C442/Rocket/Deployment mechanism/Nose Cone Inspo/images/4be0d2e7-f49b-4930-87dd-065aca3783c3.png

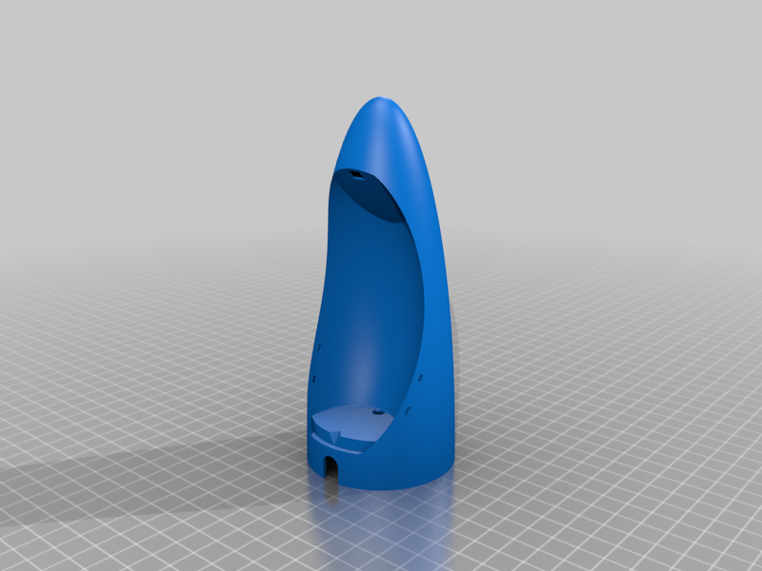
Deployment mechanism/Nose Cone Inspo/images/4be0d2e7-f49b-4930-87dd-065aca3783c3.png
