C442/Rocket/Sketches/Plan_suggestion.png

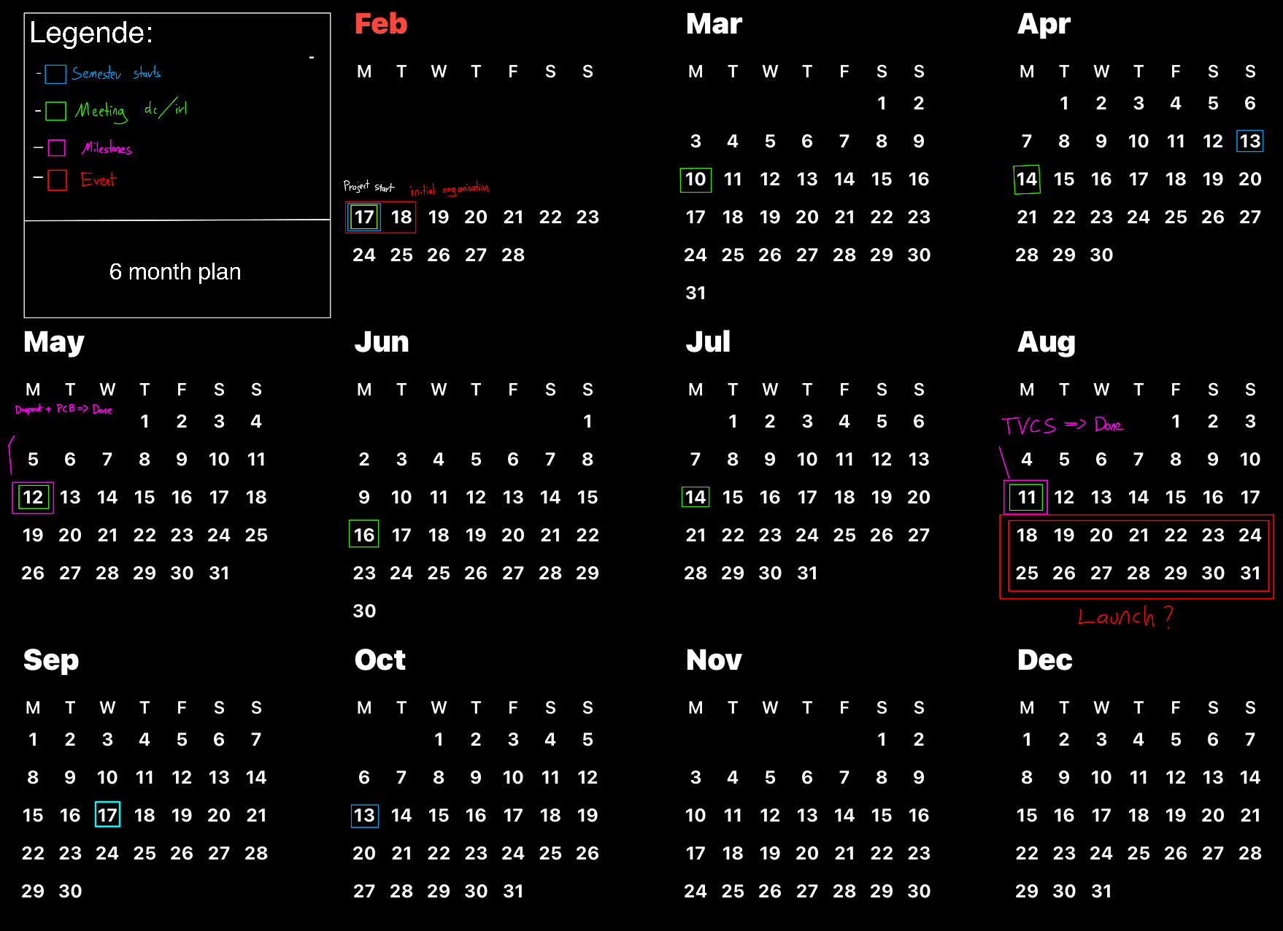
Sketches/Plan_suggestion.png
