C442/Rocket/Sketches/Sugegstion_work.png

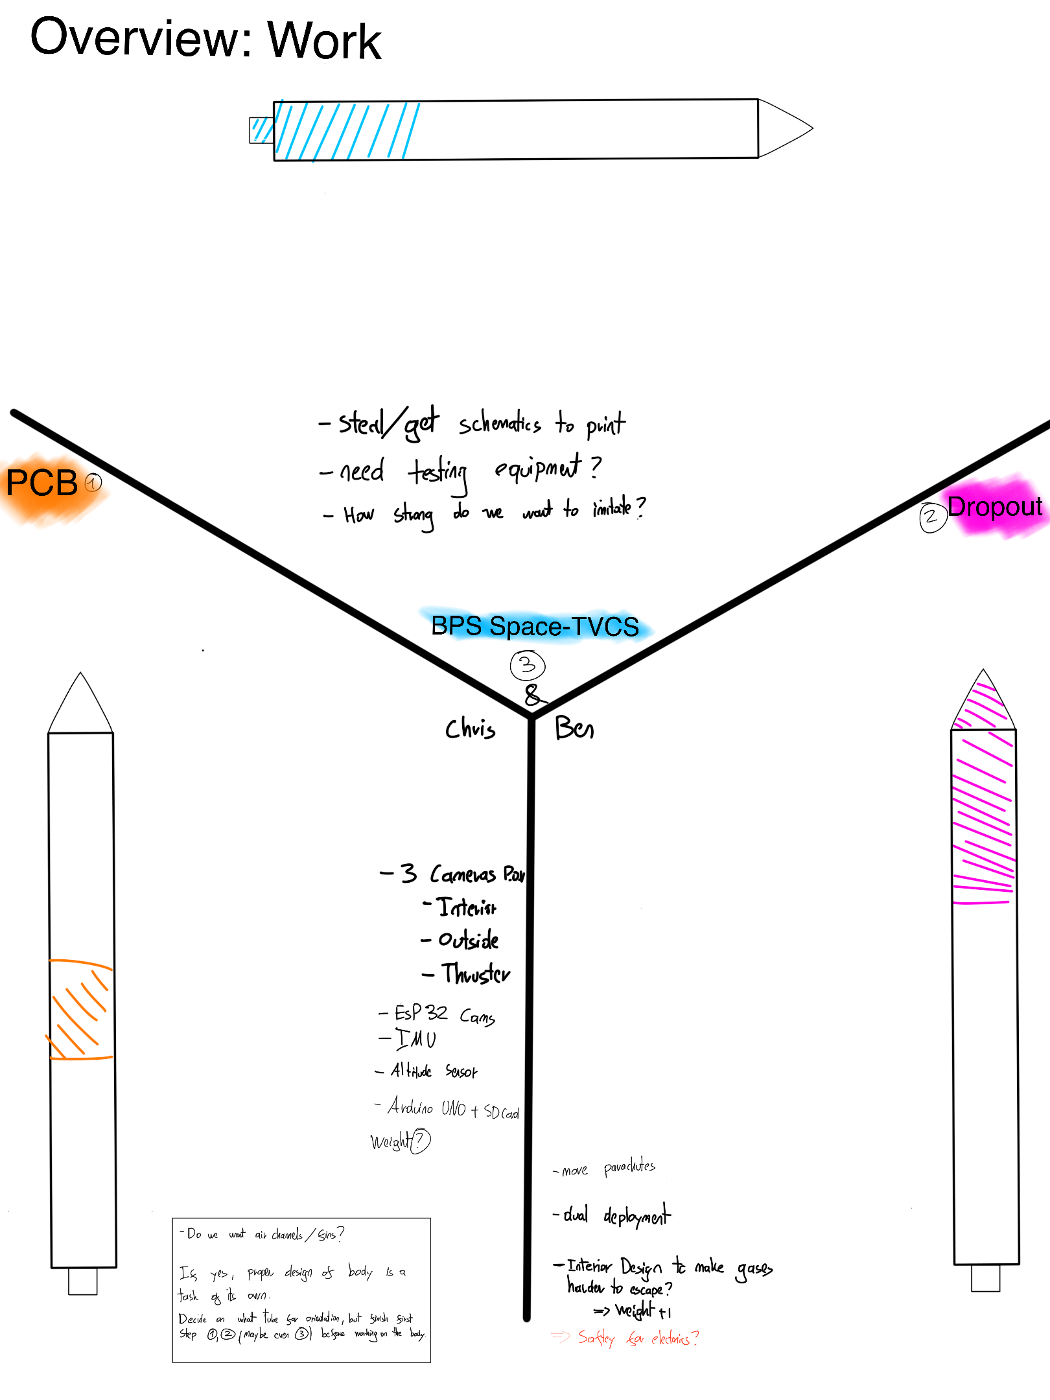
Sketches/Sugegstion_work.png
