C442/Rocket/Sketches/suggestion_visual.png

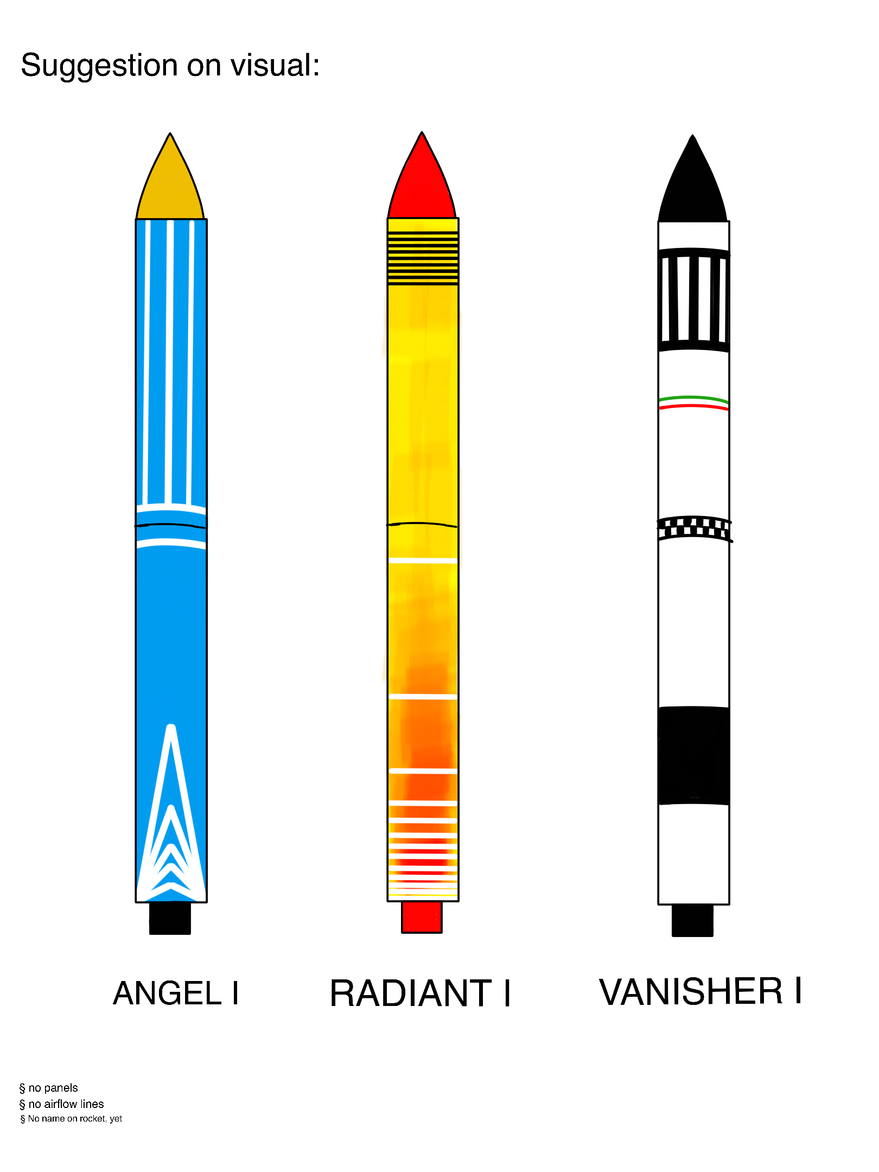
Sketches/suggestion_visual.png
