C442/Rocket/Sketches/thumbnail.jpg

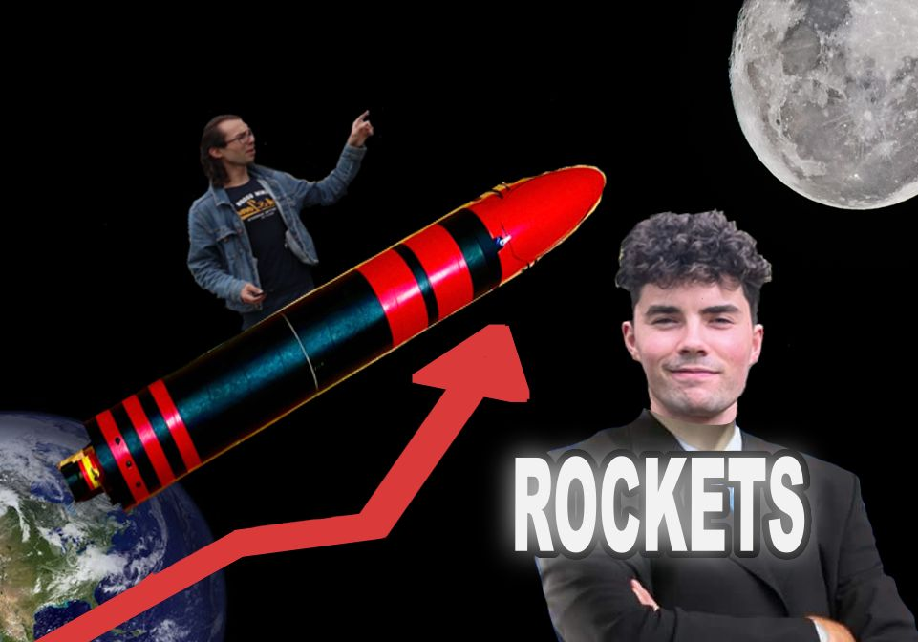
Sketches/thumbnail.jpg
