C442/Rocket/TVC/Second_PID/Inner.png

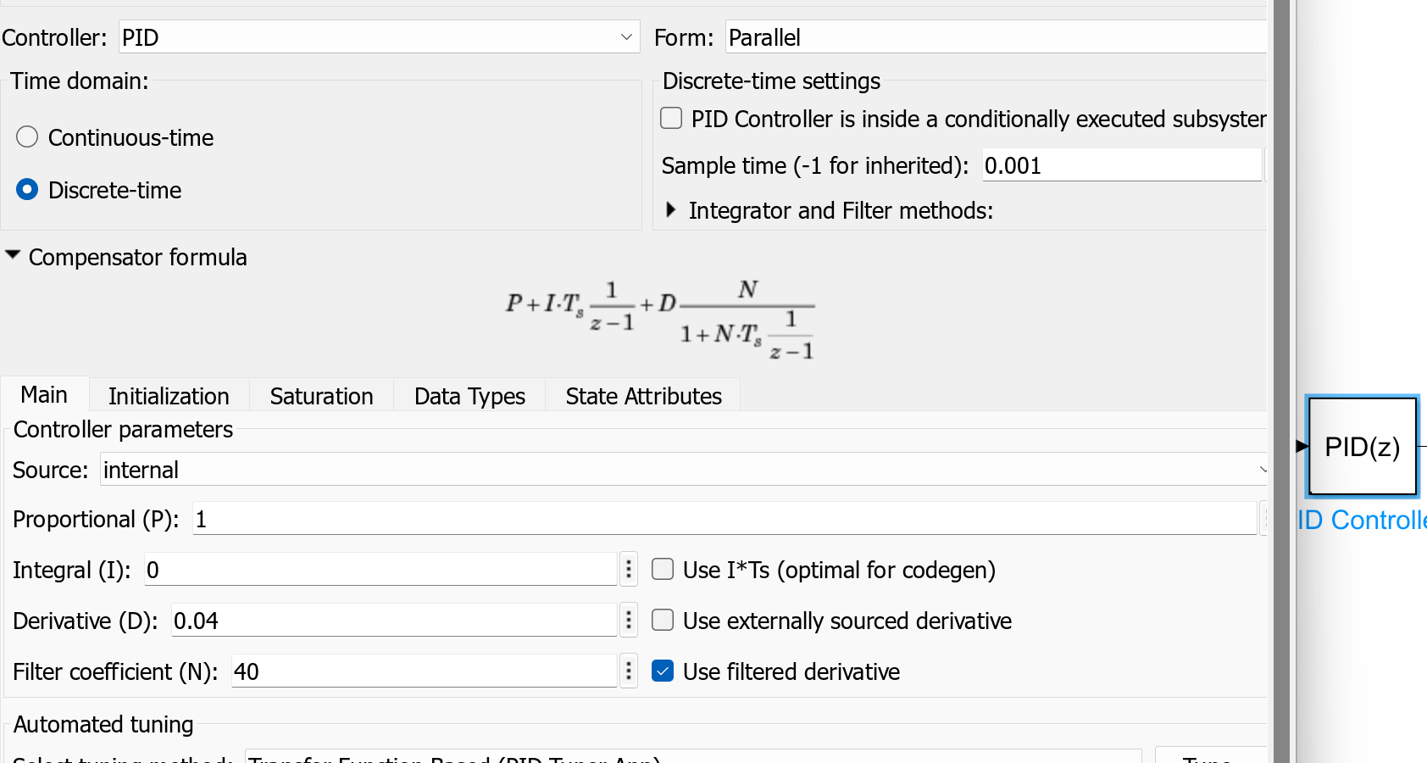
TVC/Second_PID/Inner.png
