C442/Rocket/TVC/Second_PID/Outer.png

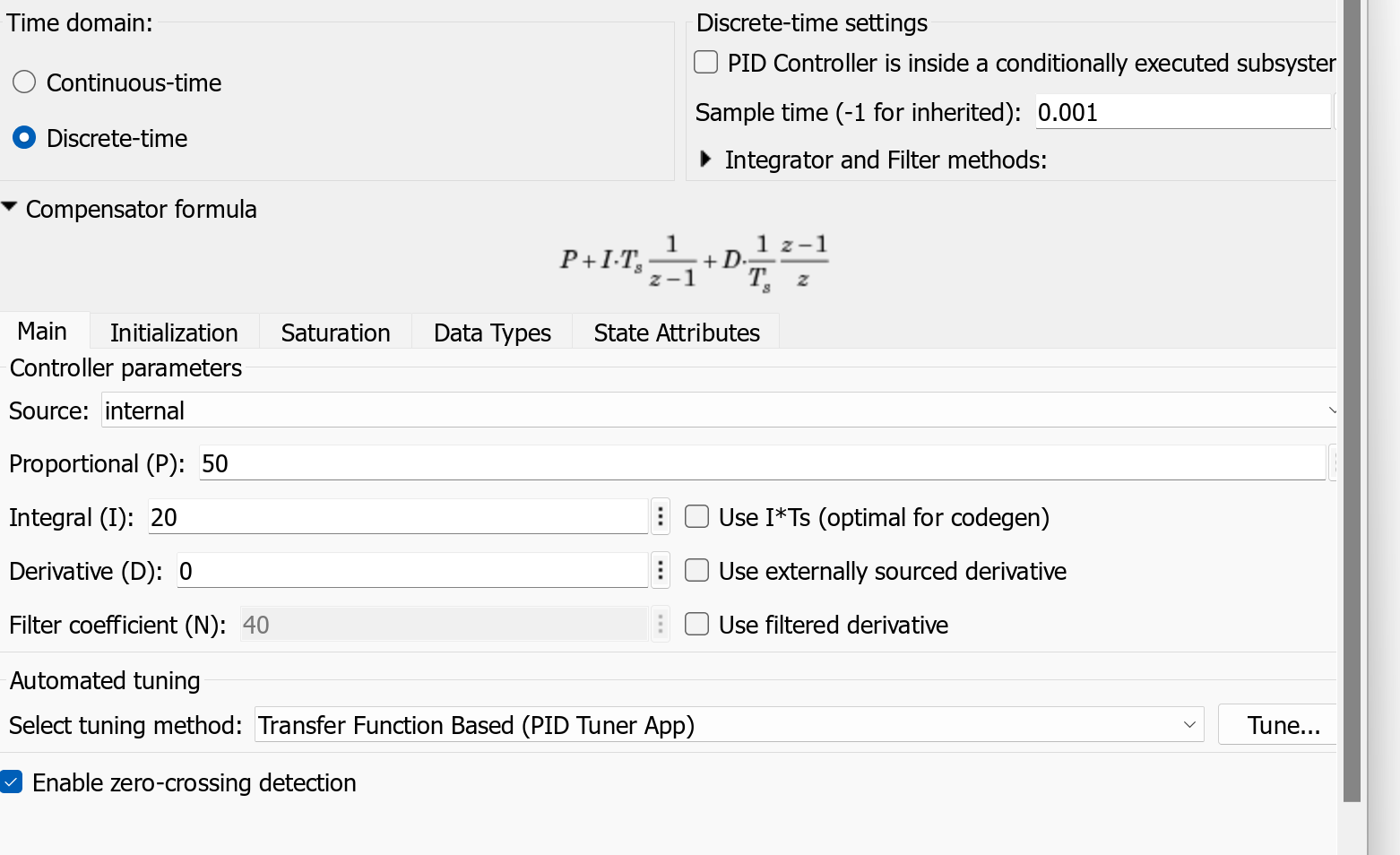
TVC/Second_PID/Outer.png
