C442/Rocket/Deployment mechanism/Nose Cone Inspo/files/retain.stl

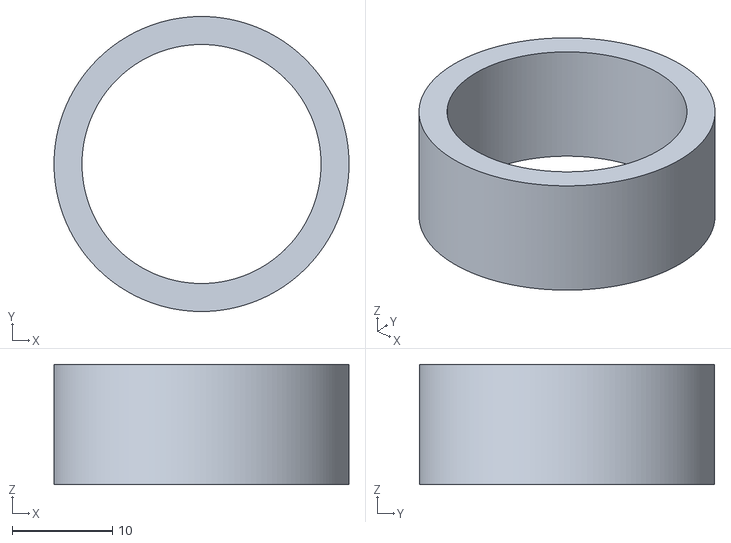
[picture p78: CAD file, 2025-03-27]
Deployment mechanism/Nose Cone Inspo/files/retain.stl
29.5 x 29.5 x 12.0
