C442/Rocket/TVC/Design/Casing.stl

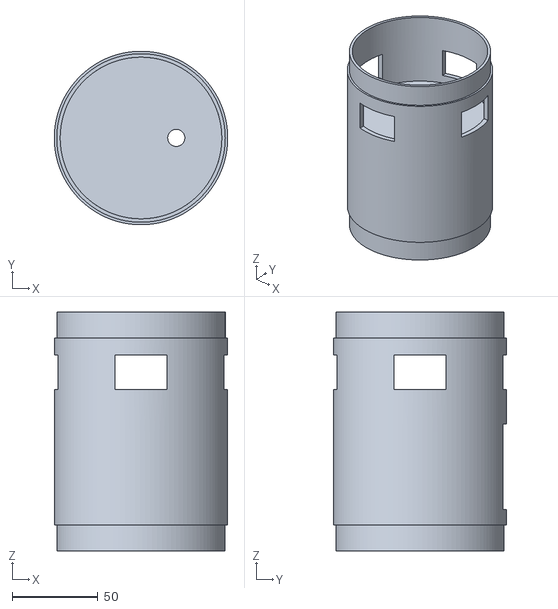
[picture p79: CAD file, 2025-04-25]
TVC/Design/Casing.stl
100.9 x 100.9 x 139.0
