C442/Rocket/Deployment mechanism/Nose Cone Adjusted 15cm/New Base.stl

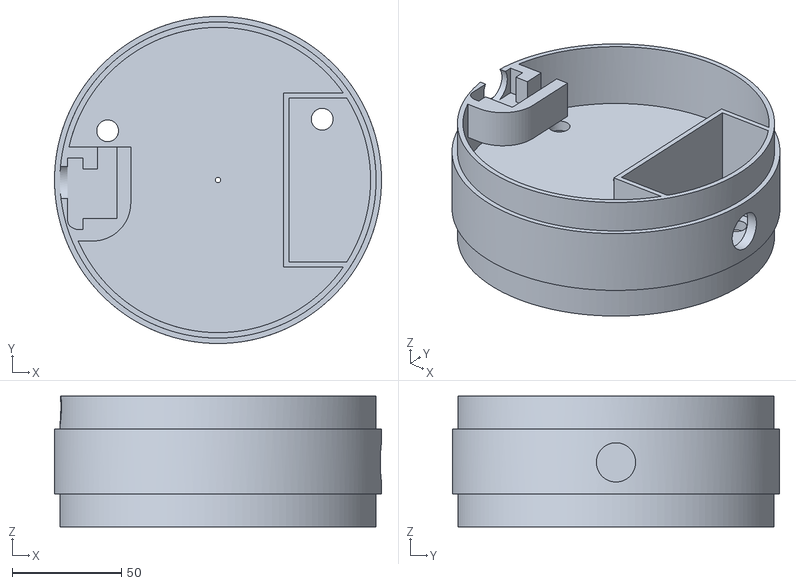
[picture p80: CAD file, 2025-03-27]
Deployment mechanism/Nose Cone Adjusted 15cm/New Base.stl
150.0 x 150.0 x 60.0
