C442/Rocket/Deployment mechanism/Nose Cone Inspo/files/New Nose Cone.stl

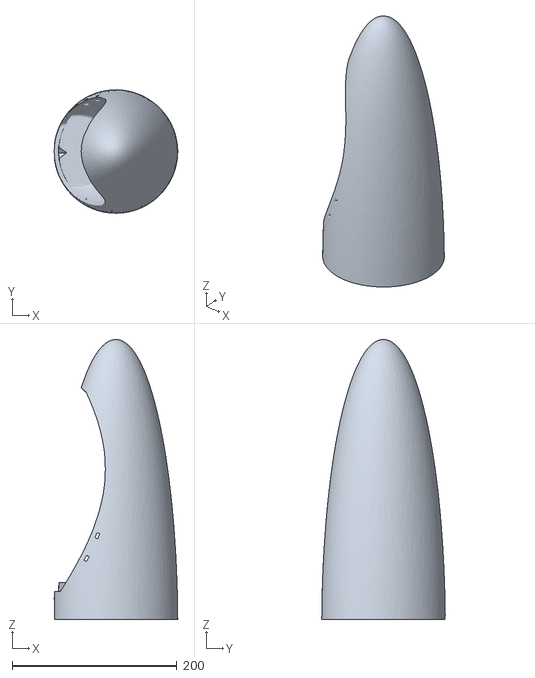
[picture p81: CAD file, 2025-03-27]
Deployment mechanism/Nose Cone Inspo/files/New Nose Cone.stl
150.0 x 150.0 x 340.0
