C442/Rocket/TVC/Design/Reaction Wheel.stl

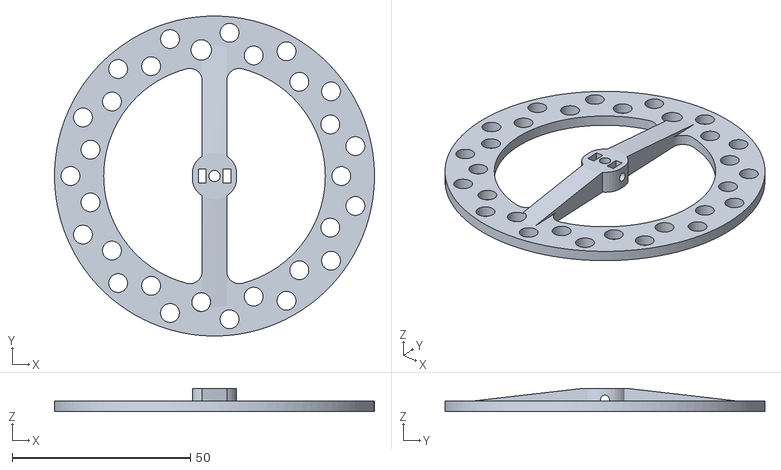
[picture p82: CAD file, 2025-04-25]
TVC/Design/Reaction Wheel.stl
89.7 x 89.7 x 6.45
