C442/Rocket/TVC/Outer Gimbal.stl

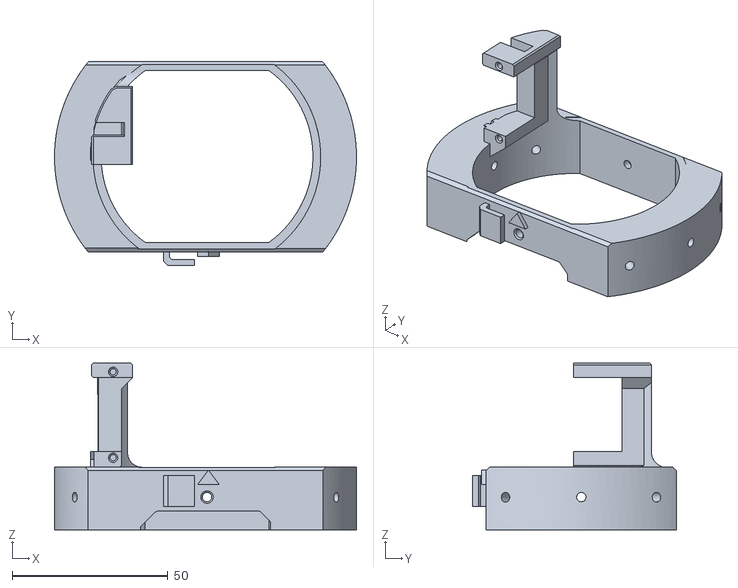
[picture p83: CAD file, 2025-04-25]
TVC/Outer Gimbal.stl
97.0 x 65.6 x 53.5
