C442/Rocket/Deployment mechanism/Nose Cone Inspo/files/payload.stl

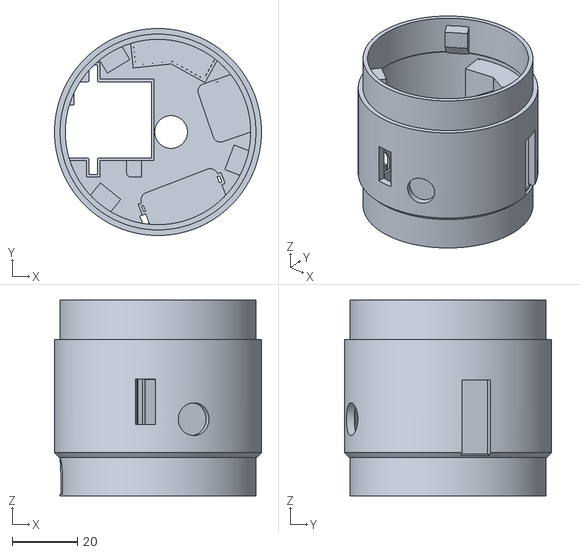
[picture p84: CAD file, 2025-03-27]
Deployment mechanism/Nose Cone Inspo/files/payload.stl
63.2 x 63.2 x 59.7
