C442/Rocket/TVC/TVC Test Stand.stl

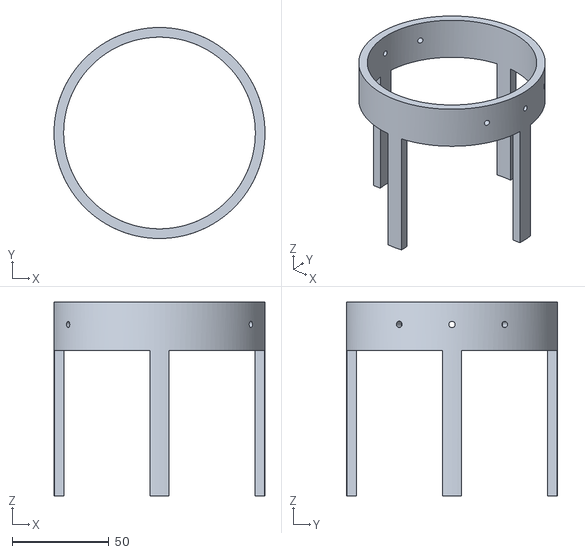
[picture p85: CAD file, 2025-04-25]
TVC/TVC Test Stand.stl
109.0 x 109.0 x 100.0
