C442/Rocket/Deployment mechanism/Nose Cone Inspo/files/60mm_closure.stl

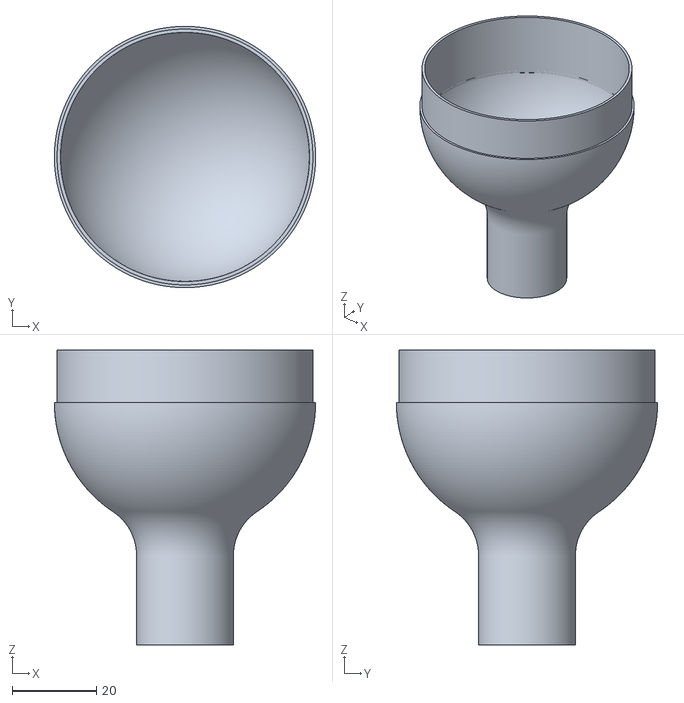
[picture p86: CAD file, 2025-03-27]
Deployment mechanism/Nose Cone Inspo/files/60mm_closure.stl
62.0 x 62.0 x 70.0
