C442/Rocket/FINAL_CODE/TVC-Flight-Code/LED.cpp

#include "LED.h"

LED::LED() {
  // Set system led pins as outputs
  pinMode(R_LED, OUTPUT);
  pinMode(G_LED, OUTPUT);
  pinMode(B_LED, OUTPUT);
}

void LED::red() {
  digitalWrite(R_LED, HIGH);
  digitalWrite(G_LED, LOW);
  digitalWrite(B_LED, LOW);
}

void LED::green() {
  digitalWrite(R_LED, LOW);
  digitalWrite(G_LED, HIGH);
  digitalWrite(B_LED, LOW);
}

void LED::blue() {
  digitalWrite(R_LED, LOW);
  digitalWrite(G_LED, LOW);
  digitalWrite(B_LED, HIGH);
}

void LED::purple() {
  digitalWrite(R_LED, HIGH);
  digitalWrite(G_LED, LOW);
  digitalWrite(B_LED, HIGH);
}

void LED::off() {
  digitalWrite(R_LED, LOW);
  digitalWrite(G_LED, LOW);
  digitalWrite(B_LED, LOW);
}
