C442/Rocket/TVC/Gyro_Testing/Gyro_Testing.ino

#include <Wire.h>
#include <Adafruit_Sensor.h>
#include <Adafruit_BNO055.h>
#include <utility/imumaths.h>
  
Adafruit_BNO055 bno = Adafruit_BNO055(55);

void setup(void) 
{
  Serial.begin(9600);
  Serial.println("Orientation Sensor Test"); Serial.println("");
  
  /* Initialise the sensor */
  if(!bno.begin())
  {
    /* There was a problem detecting the BNO055 ... check your connections */
    Serial.print("Ooops, no BNO055 detected ... Check your wiring or I2C ADDR!");
    while(1);
  }
  
  delay(1000);
    
  bno.setExtCrystalUse(true);
}

void loop(void) 
{
  imu::Vector<3> gyro = bno.getVector(Adafruit_BNO055::VECTOR_GYROSCOPE);
    
  /* Display the floating point data */
  Serial.print("X:");
  Serial.print(gyro.x());
  Serial.print(",Y:");
  Serial.print(gyro.y());
  Serial.print(",Z:");
  Serial.println(gyro.z());
  delay(100);
}
